imciner2/KiCad-Libraries/3D/0_SourceFiles/MPU9150/MPU9150-SCAD.stl

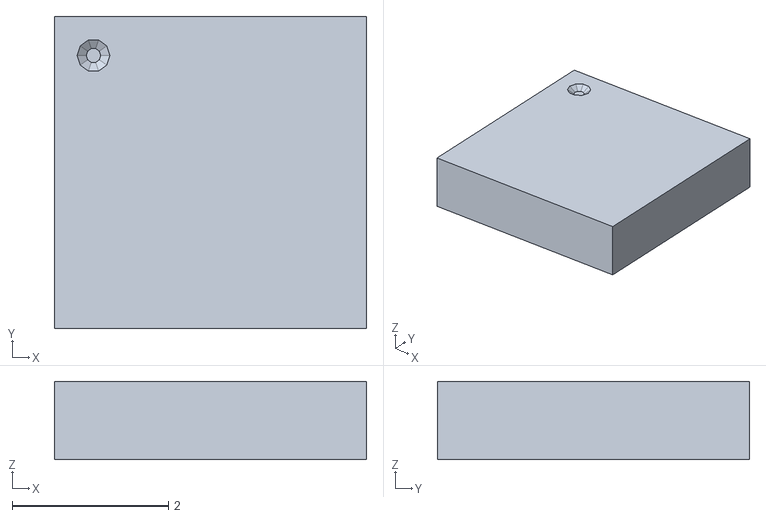
[picture p17: CAD file, 2013-07-04]
3D/0_SourceFiles/MPU9150/MPU9150-SCAD.stl
4.00 x 4.00 x 1.00
