imciner2/KiCad-Libraries/3D/0_SourceFiles/SD_Objects/SD-Amp-microSlot-Wings.stl

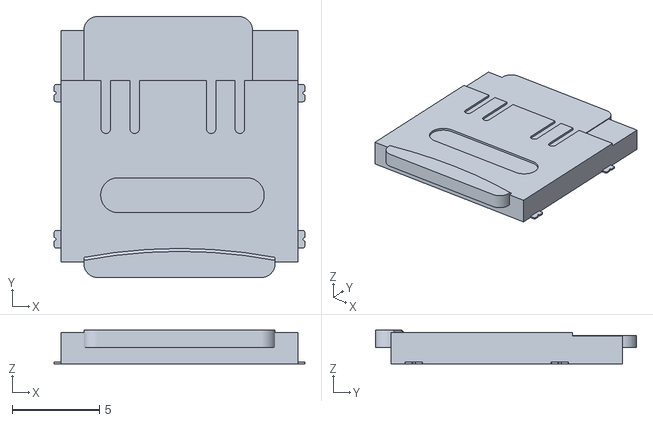
[picture p18: CAD file, 2013-07-04]
3D/0_SourceFiles/SD_Objects/SD-Amp-microSlot-Wings.stl
14.4 x 15.0 x 1.95
