imciner2/KiCad-Libraries/3D/0_SourceFiles/Sensors/SHARP_GP1A57HRJ00F-scad.stl

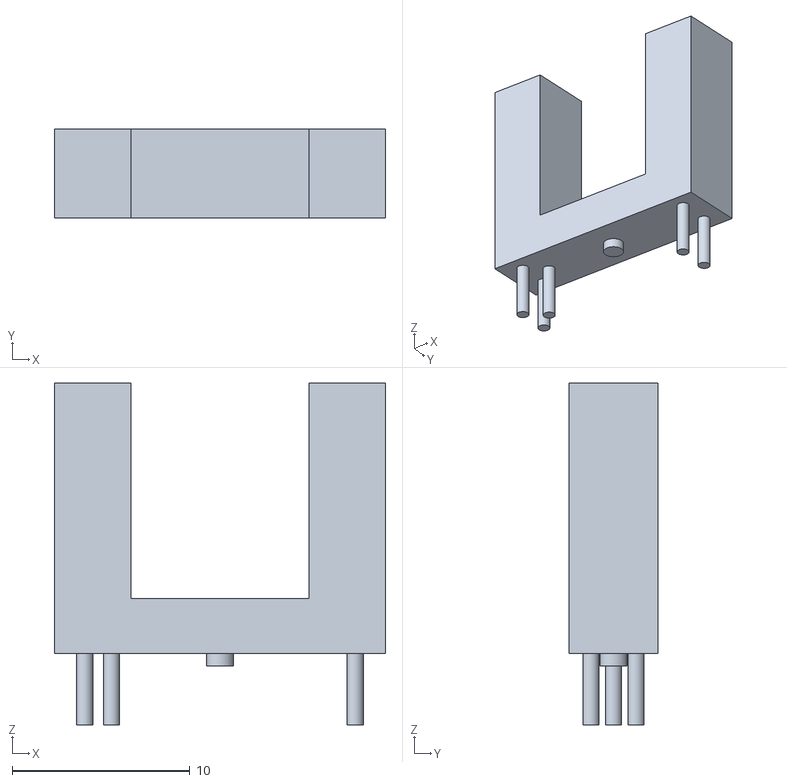
[picture p19: CAD file, 2017-01-19]
3D/0_SourceFiles/Sensors/SHARP_GP1A57HRJ00F-scad.stl
18.6 x 5.00 x 19.2
