imciner2/KiCad-Libraries/3D/0_SourceFiles/SMD_Passives/SMD-1206-scad.stl

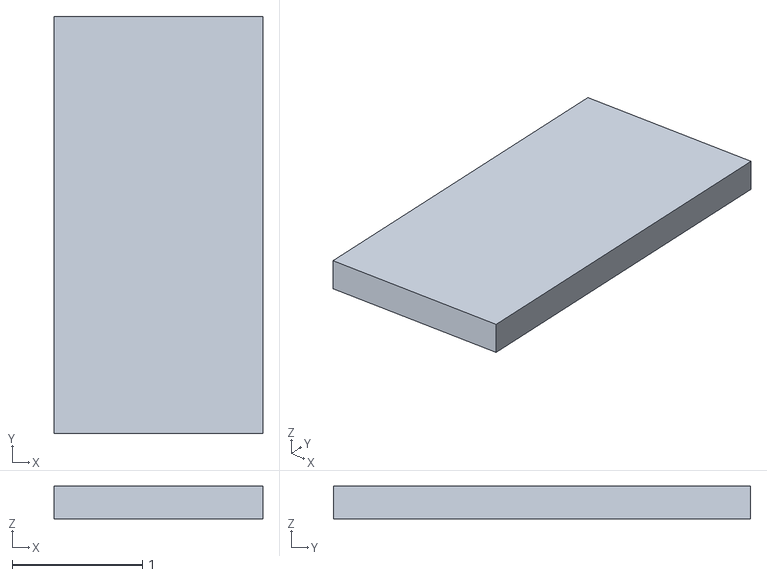
[picture p20: CAD file, 2015-03-23]
3D/0_SourceFiles/SMD_Passives/SMD-1206-scad.stl
1.60 x 3.20 x 0.25
