imciner2/KiCad-Libraries/3D/0_SourceFiles/SOIC/SOIC_08_4.0mm_5.8mm_1.27mm-wings.stl

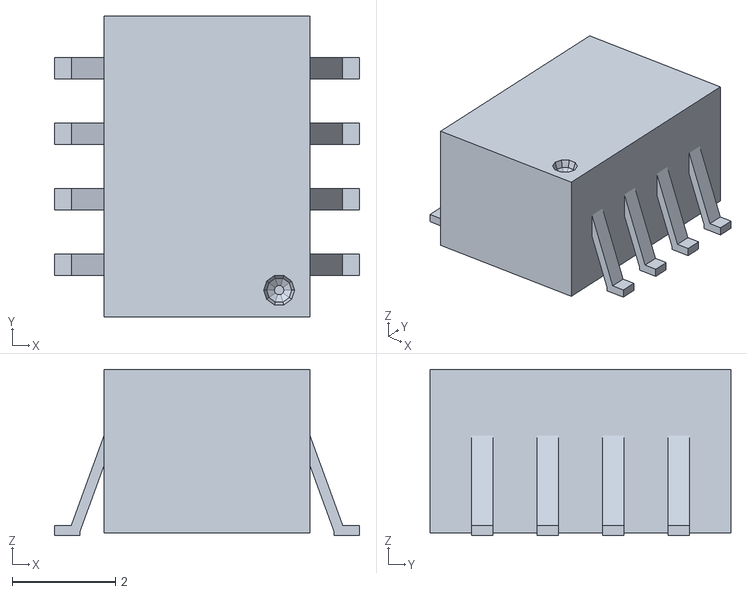
[picture p21: CAD file, 2015-07-16]
3D/0_SourceFiles/SOIC/SOIC_08_4.0mm_5.8mm_1.27mm-wings.stl
5.92 x 5.84 x 3.23
