imciner2/KiCad-Libraries/3D/0_SourceFiles/SolarCells/Spectrolab_CIC-SCAD.stl

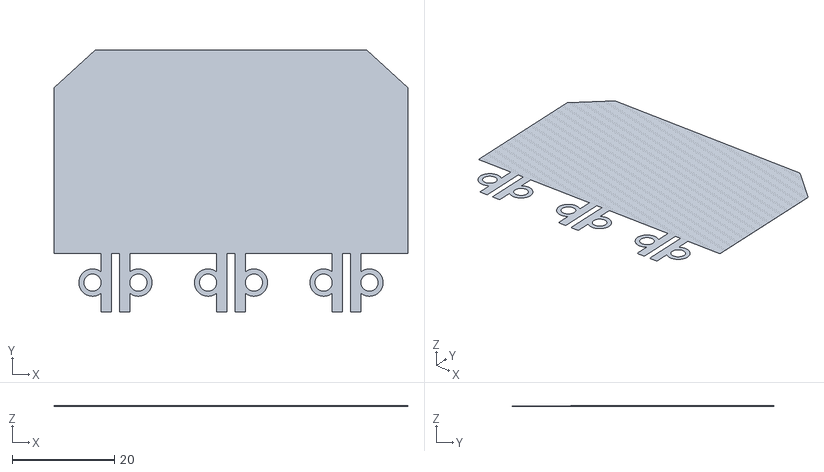
[picture p22: CAD file, 2013-12-22]
3D/0_SourceFiles/SolarCells/Spectrolab_CIC-SCAD.stl
69.1 x 51.1 x 0.178
