imciner2/KiCad-Libraries/3D/0_SourceFiles/SON-10/SON-10-scad.stl

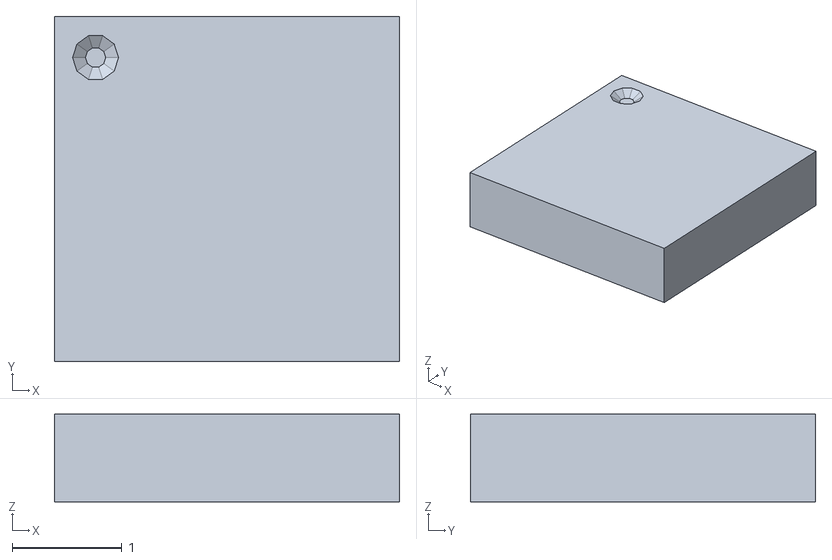
[picture p23: CAD file, 2013-10-12]
3D/0_SourceFiles/SON-10/SON-10-scad.stl
3.15 x 3.15 x 0.8
