imciner2/KiCad-Libraries/3D/0_SourceFiles/SOT-23/SOT-23-6-wings.stl

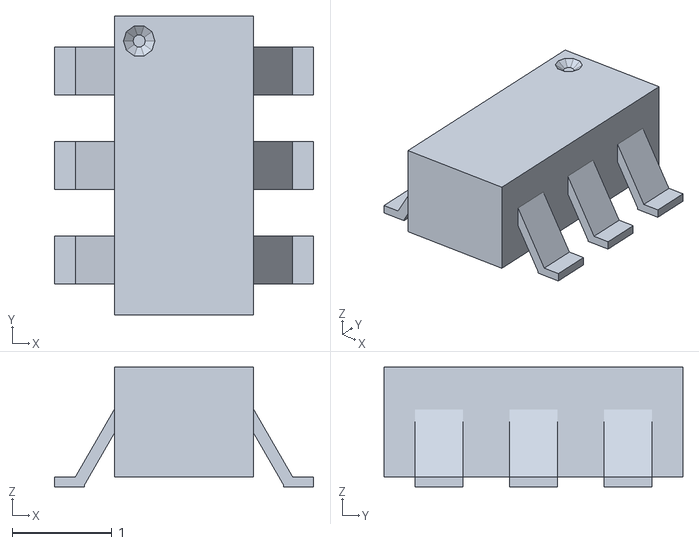
[picture p24: CAD file, 2015-07-16]
3D/0_SourceFiles/SOT-23/SOT-23-6-wings.stl
2.60 x 3.00 x 1.20
