imciner2/KiCad-Libraries/3D/0_SourceFiles/SOT-363/SOT-363-Wings.stl

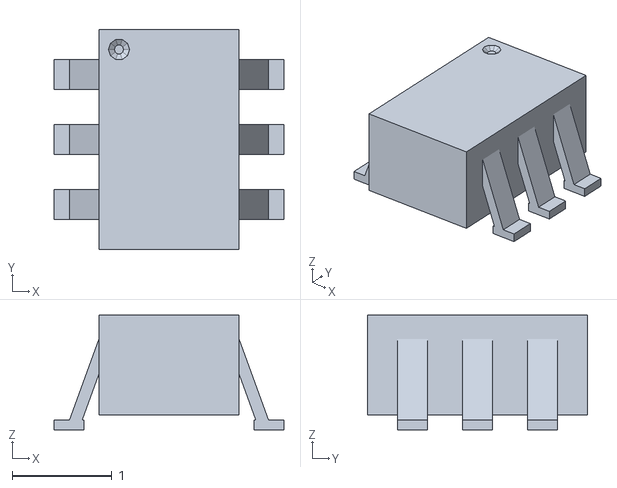
[picture p25: CAD file, 2013-07-04]
3D/0_SourceFiles/SOT-363/SOT-363-Wings.stl
2.30 x 2.20 x 1.15
