imciner2/KiCad-Libraries/3D/0_SourceFiles/Switches/Switch-DIP-SMD-3-Wings.stl

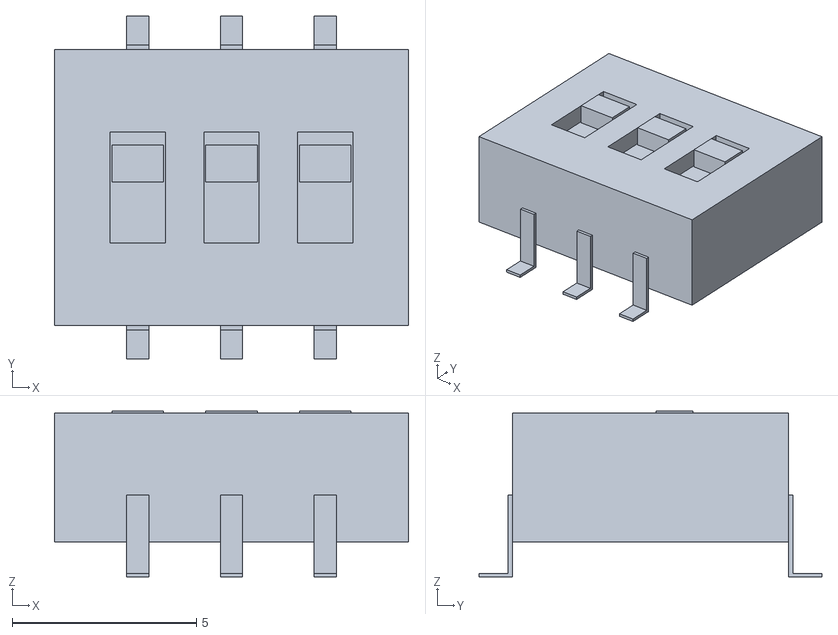
[picture p27: CAD file, 2013-07-04]
3D/0_SourceFiles/Switches/Switch-DIP-SMD-3-Wings.stl
9.60 x 9.30 x 4.50
