imciner2/KiCad-Libraries/3D/0_SourceFiles/Venus638/Venus638-SCAD.stl

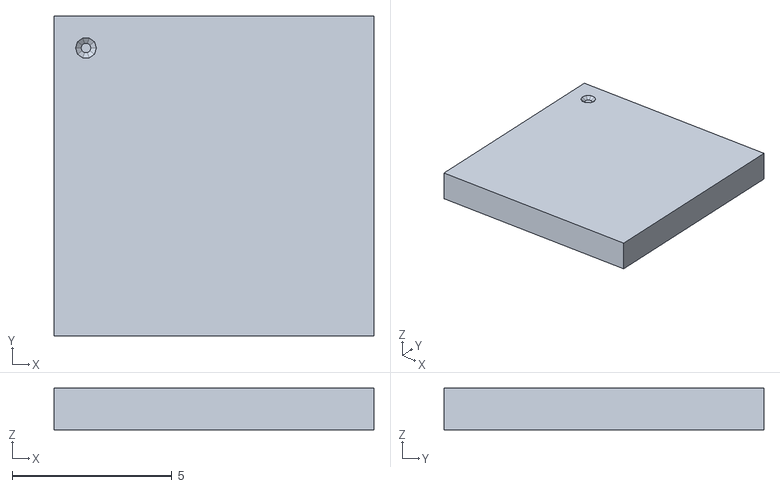
[picture p28: CAD file, 2013-07-04]
3D/0_SourceFiles/Venus638/Venus638-SCAD.stl
10.0 x 10.0 x 1.30
