imciner2/KiCad-Libraries/3D/0_SourceFiles/Connectors/CONN_1x6/CONN_1x6_Female.stl

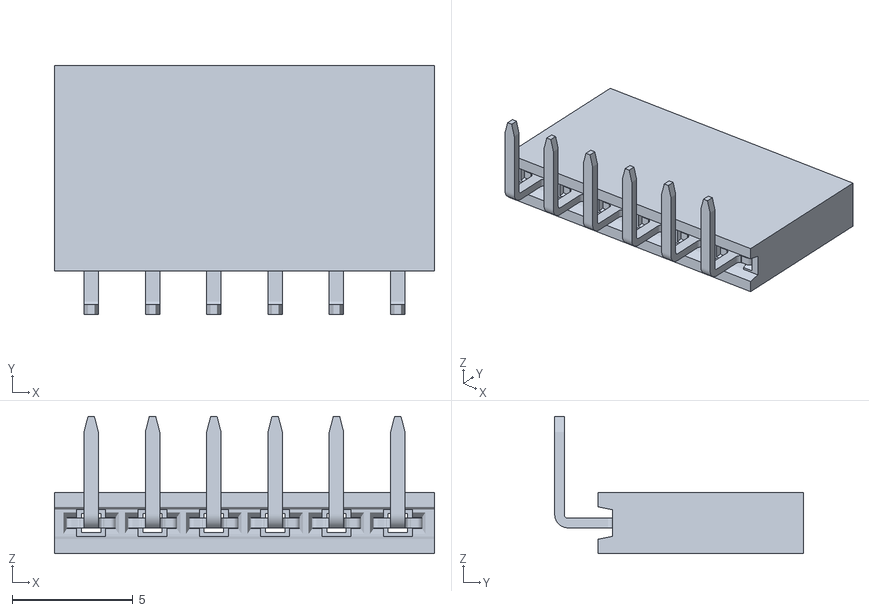
[picture p29: CAD file, 2015-07-16]
3D/0_SourceFiles/Connectors/CONN_1x6/CONN_1x6_Female.stl
15.7 x 10.3 x 5.69
