imciner2/KiCad-Libraries/3D/0_SourceFiles/Connectors/CONN_2x6/CONN_2x6_Female.stl

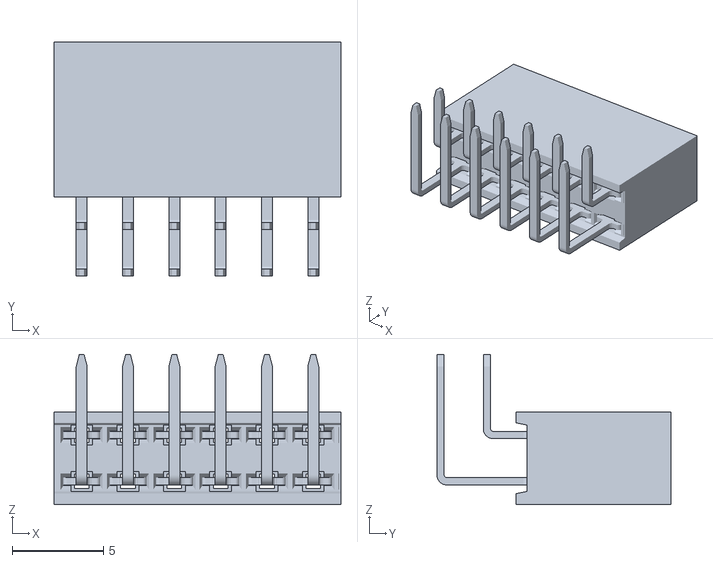
[picture p30: CAD file, 2015-07-16]
3D/0_SourceFiles/Connectors/CONN_2x6/CONN_2x6_Female.stl
15.7 x 12.8 x 8.23
