imciner2/KiCad-Libraries/3D/0_SourceFiles/Connectors/SAMTEC_TFM-115-01-F-D-A/TFM-115-01-F-D-A-wings.stl

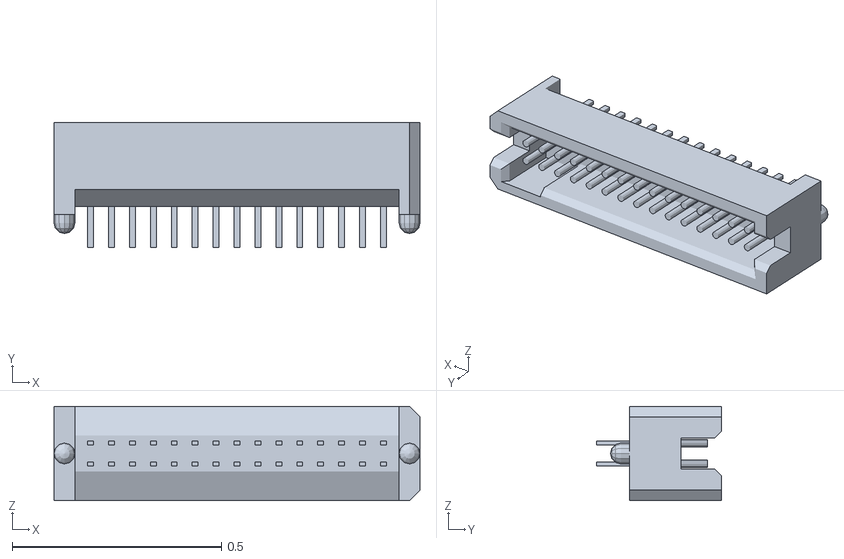
[picture p31: CAD file, 2017-06-12]
3D/0_SourceFiles/Connectors/SAMTEC_TFM-115-01-F-D-A/TFM-115-01-F-D-A-wings.stl
0.875 x 0.298 x 0.225
