imciner2/KiCad-Libraries/3D/0_SourceFiles/SMD_Passives/SMD-0805-scad.stl

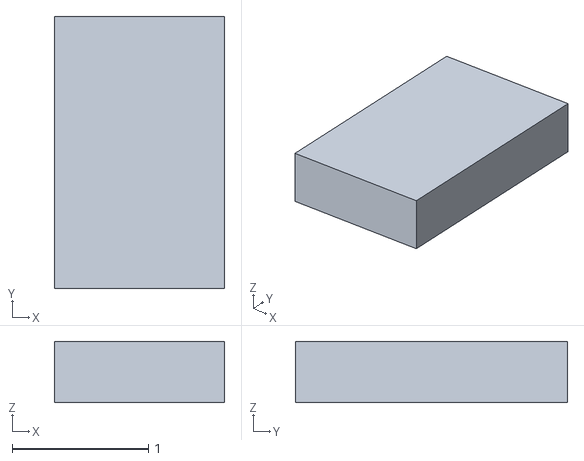
[picture p33: CAD file, 2015-03-23]
3D/0_SourceFiles/SMD_Passives/SMD-0805-scad.stl
1.25 x 2.00 x 0.45
