imciner2/KiCad-Libraries/3D/0_SourceFiles/SOIC/SOIC_08_4.0mm_5.0mm_1.27mm-scad.stl

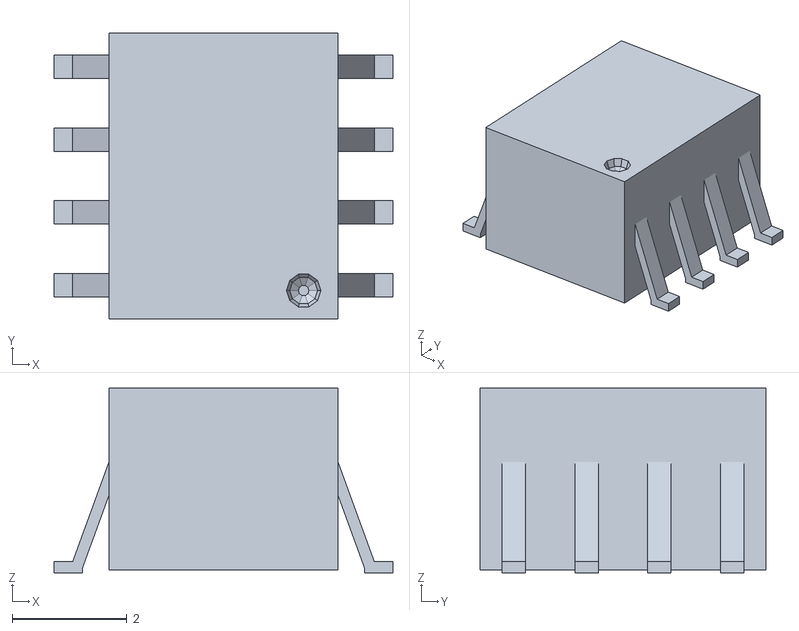
[picture p34: CAD file, 2015-07-16]
3D/0_SourceFiles/SOIC/SOIC_08_4.0mm_5.0mm_1.27mm-scad.stl
5.92 x 5.00 x 3.23
