imciner2/KiCad-Libraries/3D/0_SourceFiles/SON-10/SON-10-wings.stl

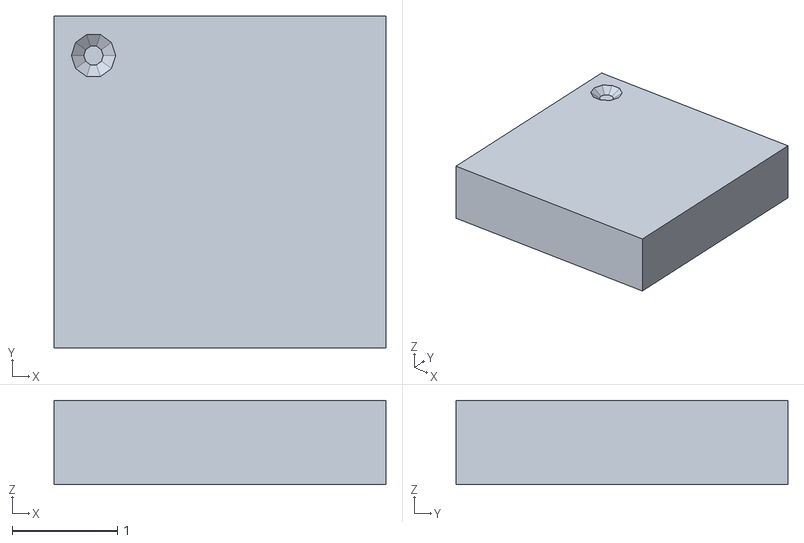
[picture p35: CAD file, 2013-10-12]
3D/0_SourceFiles/SON-10/SON-10-wings.stl
3.15 x 3.15 x 0.8
