imciner2/KiCad-Libraries/3D/0_SourceFiles/Connectors/Deans/Deans-Wings.stl

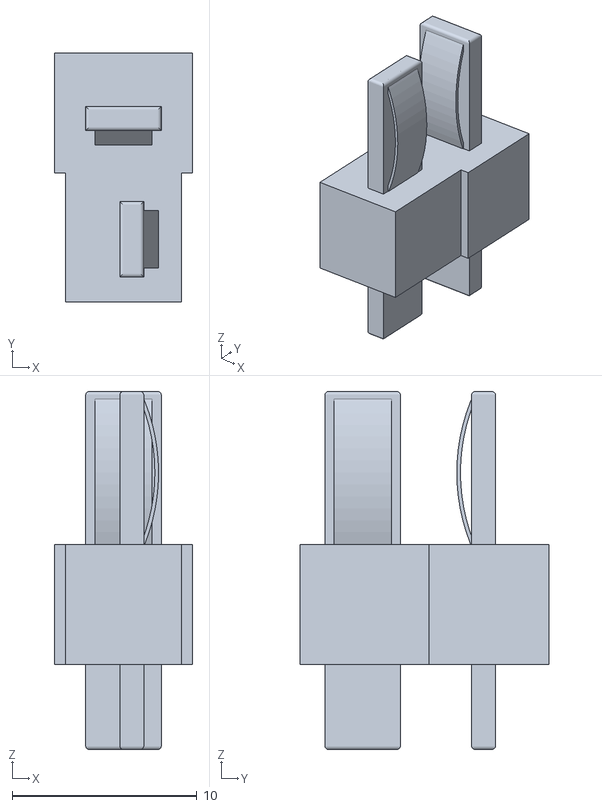
[picture p36: CAD file, 2013-07-04]
3D/0_SourceFiles/Connectors/Deans/Deans-Wings.stl
7.50 x 13.5 x 19.4
