imciner2/KiCad-Libraries/3D/0_SourceFiles/SMD_Passives/SMD-2010-scad.stl

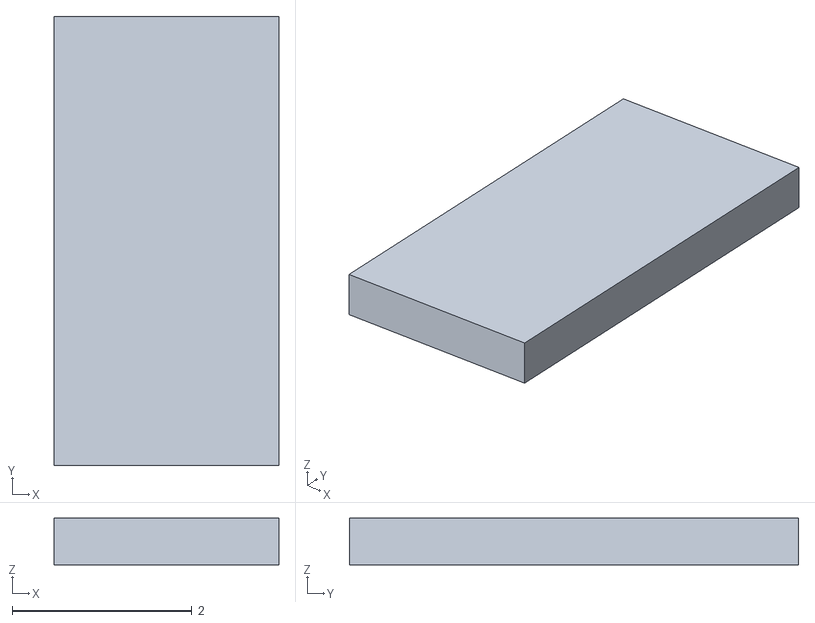
[picture p37: CAD file, 2015-03-23]
3D/0_SourceFiles/SMD_Passives/SMD-2010-scad.stl
2.50 x 5.00 x 0.52
