imciner2/KiCad-Libraries/3D/0_SourceFiles/SolarCells/Spectrolab_TASC1-SCAD.stl

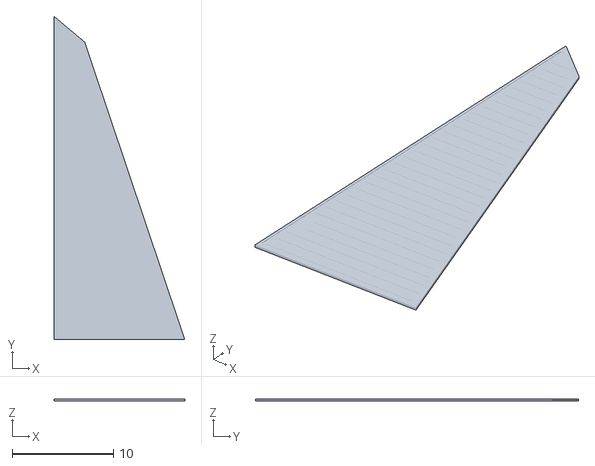
[picture p38: CAD file, 2013-07-04]
3D/0_SourceFiles/SolarCells/Spectrolab_TASC1-SCAD.stl
12.9 x 31.9 x 0.178
