imciner2/KiCad-Libraries/3D/0_SourceFiles/SSOP/SSOP_20_4.5mm_6.6mm_0.65mm-wings.stl

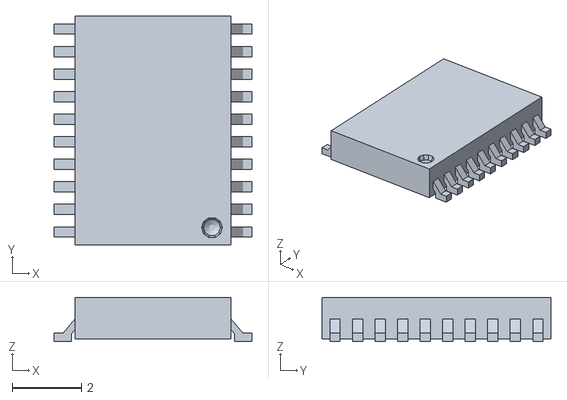
[picture p39: CAD file, 2015-07-16]
3D/0_SourceFiles/SSOP/SSOP_20_4.5mm_6.6mm_0.65mm-wings.stl
5.70 x 6.60 x 1.28
