imciner2/KiCad-Libraries/3D/0_SourceFiles/Switches/Switch-Eswitch-Slide-SCAD.stl

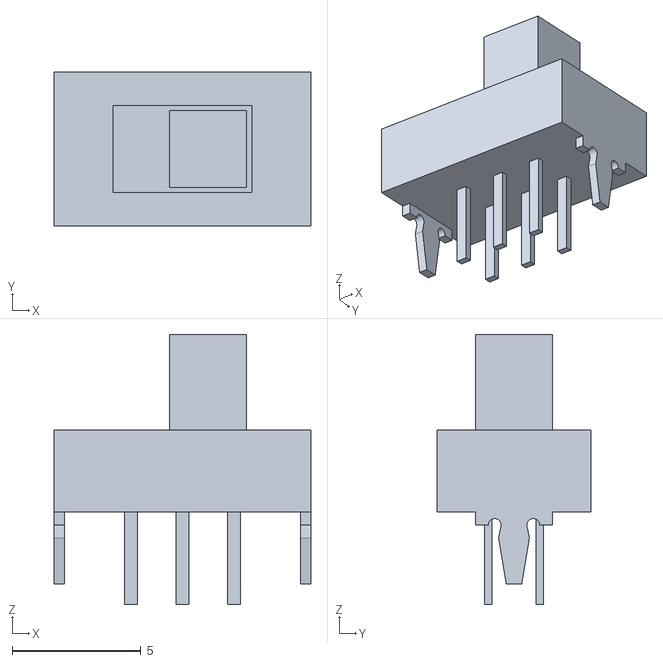
[picture p40: CAD file, 2013-07-04]
3D/0_SourceFiles/Switches/Switch-Eswitch-Slide-SCAD.stl
10.0 x 6.00 x 10.5
