imciner2/KiCad-Libraries/3D/0_SourceFiles/SSOP/SSOP_08_3.0mm_3.0mm_0.65mm-scad.stl

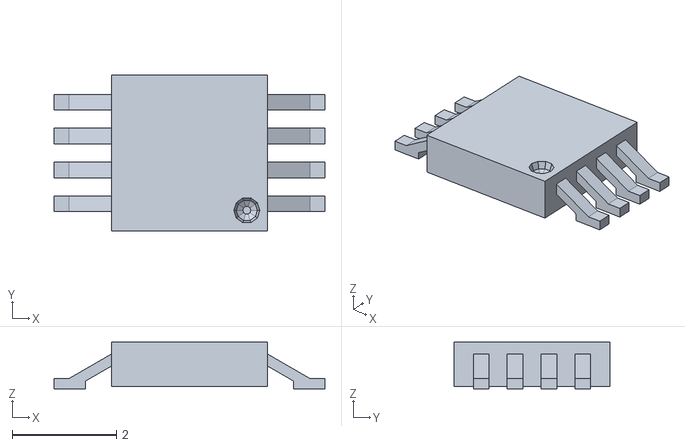
[picture p41: CAD file, 2015-07-16]
3D/0_SourceFiles/SSOP/SSOP_08_3.0mm_3.0mm_0.65mm-scad.stl
5.20 x 3.00 x 0.9
