imciner2/KiCad-Libraries/3D/0_SourceFiles/Switches/Switch-TE-Slide-SCAD.stl

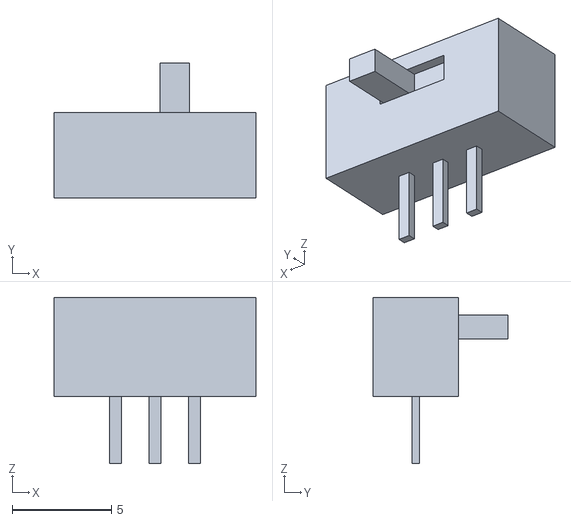
[picture p42: CAD file, 2013-07-04]
3D/0_SourceFiles/Switches/Switch-TE-Slide-SCAD.stl
10.2 x 6.80 x 8.40
