imciner2/KiCad-Libraries/3D/0_SourceFiles/SMD_Passives/SMD-0805.scad

/*
 * Create a 0805 size case
 *
 * Author: Ian McInerney
 * Created: March 19, 2015
 */

// The case
translate([0, 0, 0.45/2]){
	cube(size=[1.25,2.0,0.45], center=true);
}
