imciner2/KiCad-Libraries/3D/0_SourceFiles/SMD_Passives/SMD-1206.scad

/*
 * Creates a 1206 size passive
 *
 * Author: Ian McInerney
 * Created: March 23, 2015
 */

// The object
translate([0, 0, 0.125] ) {
	cube(size=[1.6,3.2,0.25], center=true);
}
