imciner2/KiCad-Libraries/3D/0_SourceFiles/SMD_Passives/SMD-2010.scad

/*
 * Create a 2010 size case
 *
 * Author: Ian McInerney
 * Created: March 19, 2015
 */

// The case
translate([0,0,0.52/2]) {
	cube(size=[2.5,5.0,0.52], center=true);
}
